amirt01/Balancing-Robot/CAD/98689A113_General Purpose 18-8 Stainless Steel Washer.SLDPRT

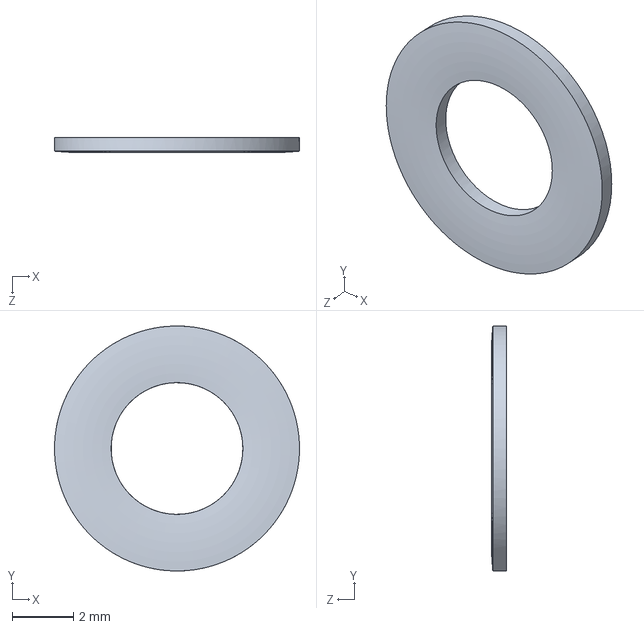
[picture p15: CAD file, 2023-06-29]
CAD/98689A113_General Purpose 18-8 Stainless Steel Washer.SLDPRT
8.00 x 8.00 x 0.5 mm
