amirt01/Balancing-Robot/CAD/2726N61_Medium Density Fiberboard Sheet.SLDPRT

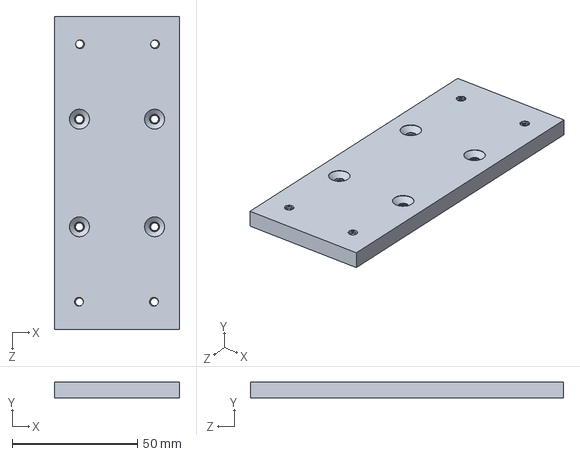
[picture p16: CAD file, 2023-06-29]
CAD/2726N61_Medium Density Fiberboard Sheet.SLDPRT
50.0 x 6.35 x 125.0 mm
